thatdecade/Multiple-USB-RGB-Power-Lighting/photos/Under Cabinet Puck Light.jpg

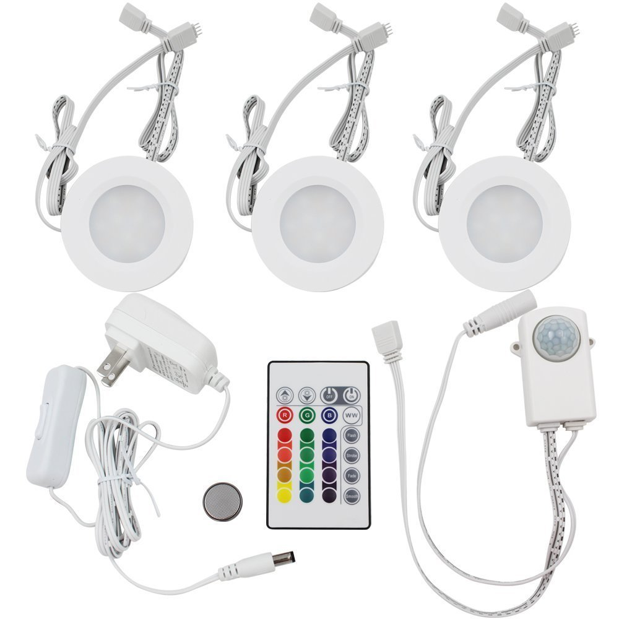
photos/Under Cabinet Puck Light.jpg
