thatdecade/Multiple-USB-RGB-Power-Lighting/photos/puck_wiring.jpg

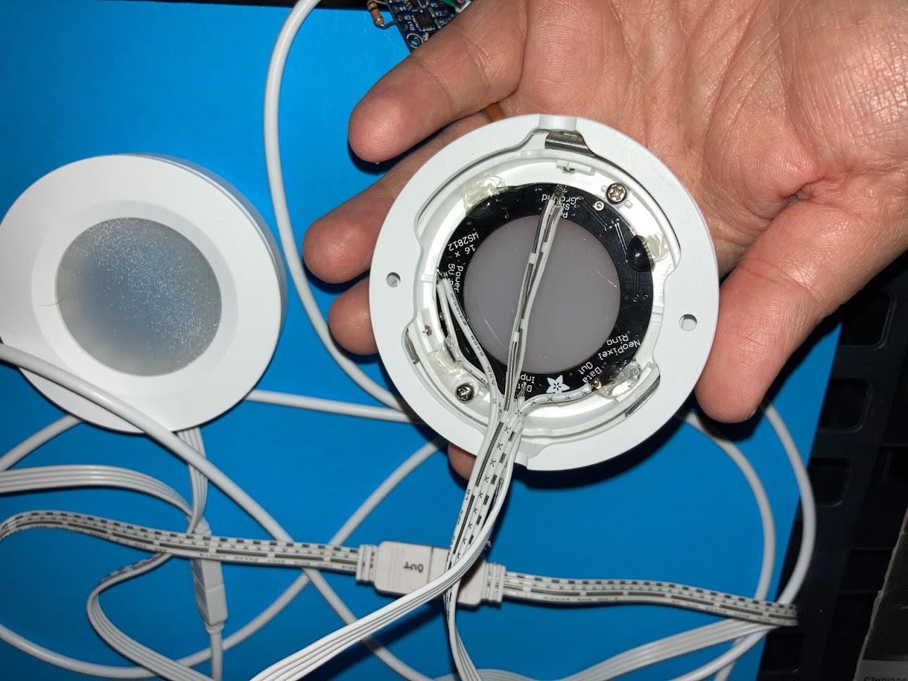
photos/puck_wiring.jpg
